Rau7han/ESP32-Home-Automation-Control-Panel-/media/photos/display_module_front.webp

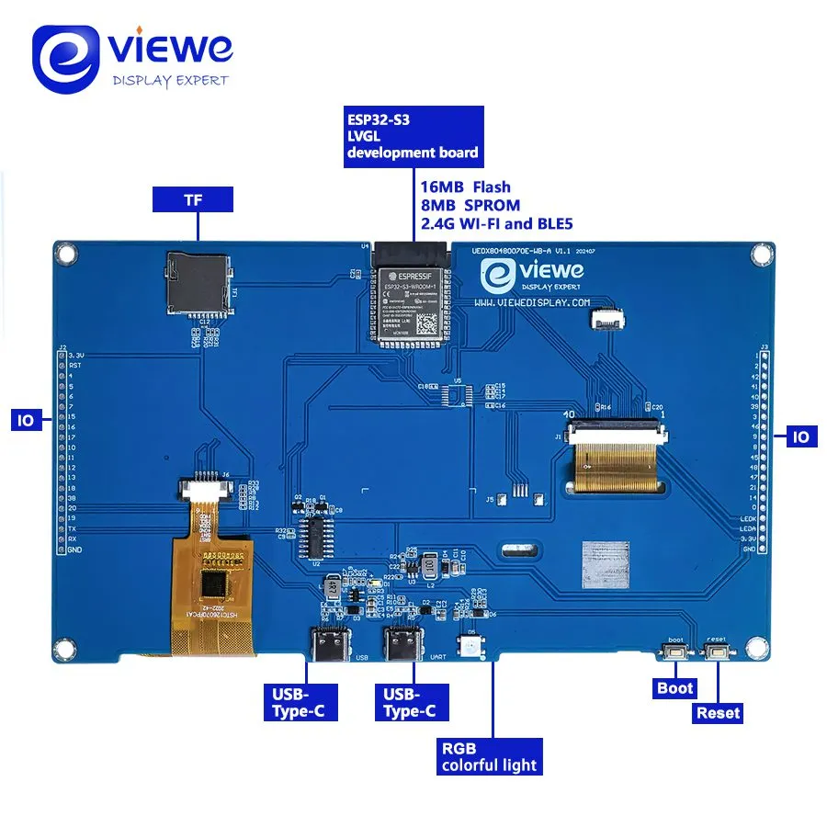
media/photos/display_module_front.webp
