Rau7han/ESP32-Home-Automation-Control-Panel-/media/photos/espnow_communication.png

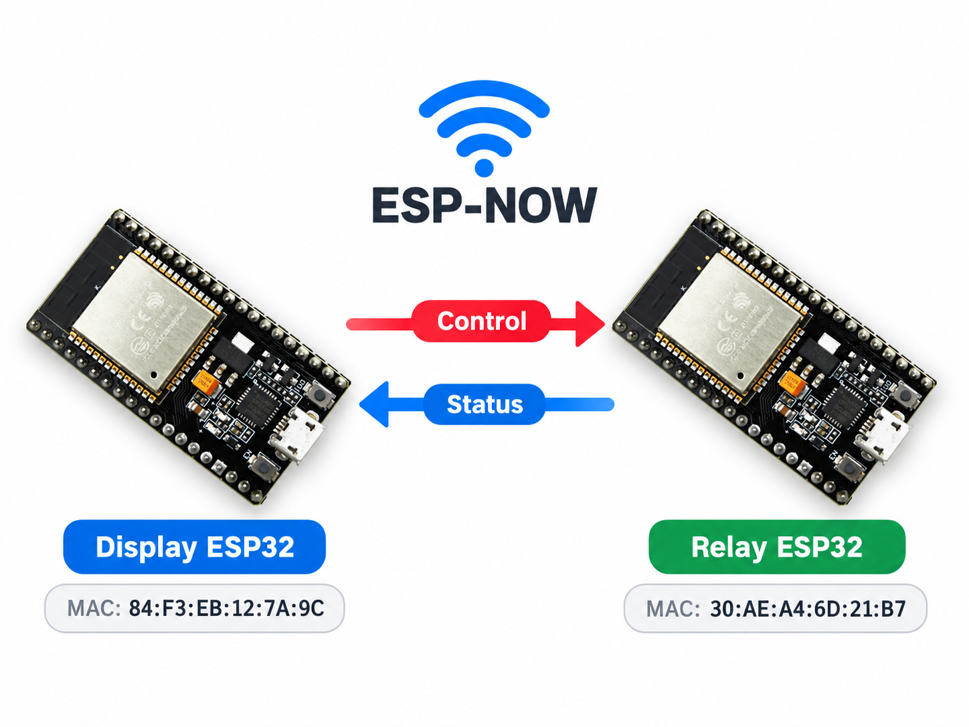
media/photos/espnow_communication.png
