Rau7han/ESP32-Home-Automation-Control-Panel-/media/photos/viewe_display_module.png

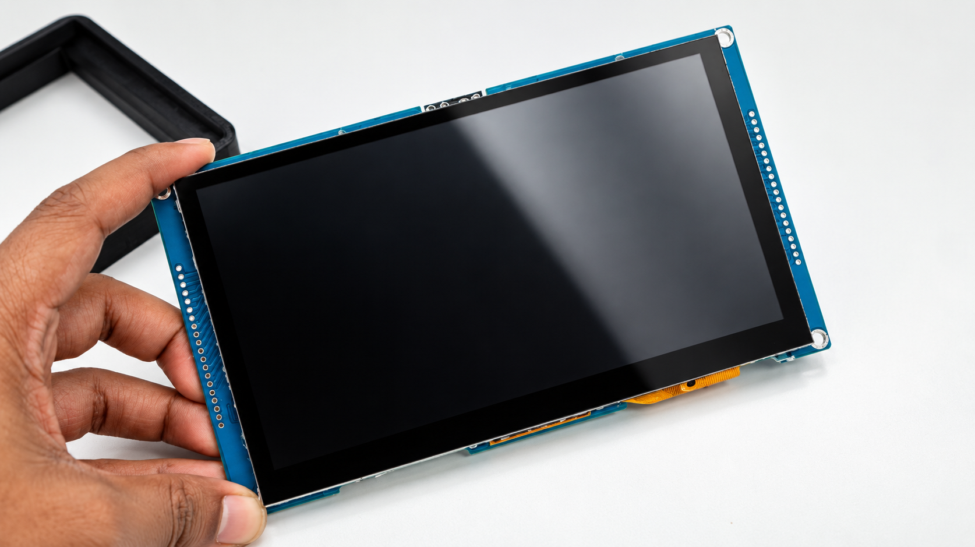
media/photos/viewe_display_module.png
