Rau7han/ESP32-Home-Automation-Control-Panel-/media/photos/wall_mount_panel.png

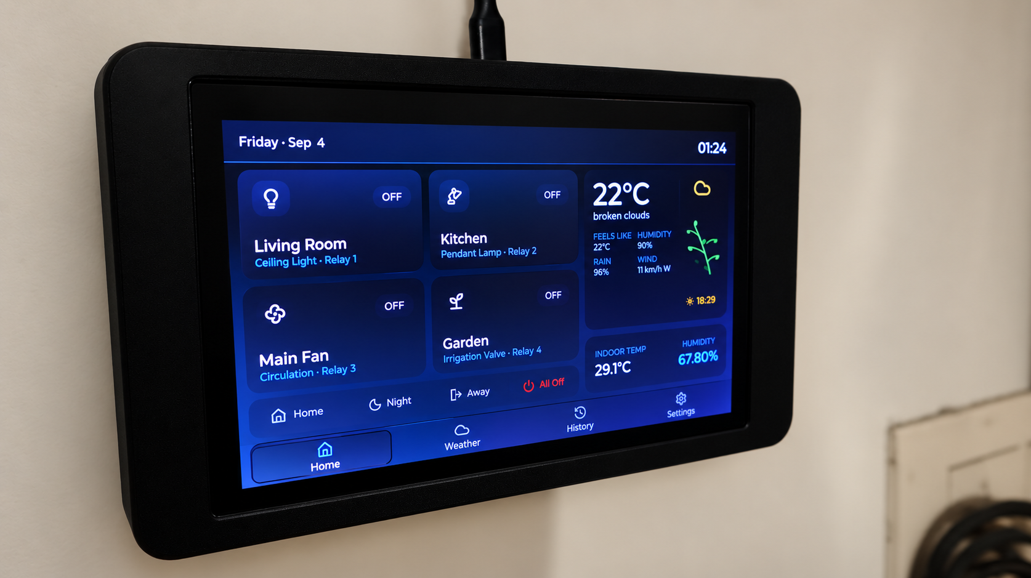
media/photos/wall_mount_panel.png
