Rau7han/ESP32-Home-Automation-Control-Panel-/media/photos/esp32_history.png

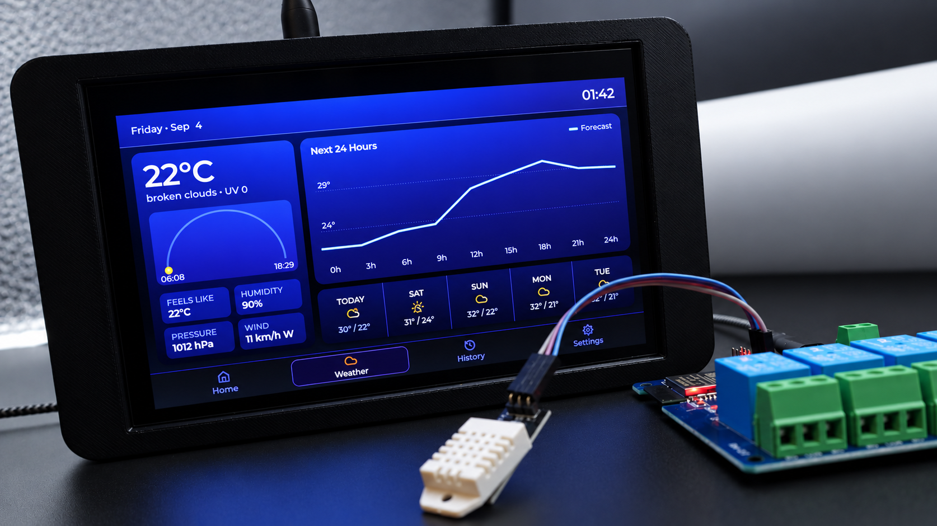
media/photos/esp32_history.png
