Rau7han/ESP32-Home-Automation-Control-Panel-/source-code/smart-panel-display/secrets.h

#pragma once

#define WIFI_SSID          "ESP"
#define WIFI_PASSWORD      "abcd1234"

#define OPENWEATHER_KEY    "2ad9388c2b289027a656451b1c14db5d"

#define WEATHER_LATITUDE   "12.9762"
#define WEATHER_LONGITUDE  "77.6033"

/* Replace with the local POSIX timezone, for example "IST-5:30". */
#define TIMEZONE_INFO      "IST-5:30"
